MustBeArt/Zorba-composite-video/Zorba composite adapter/Zorba composite adapter.kicad_sch

## KiCad design Zorba composite adapter/Zorba composite adapter.kicad_sch (2023-02-18, an earlier design)

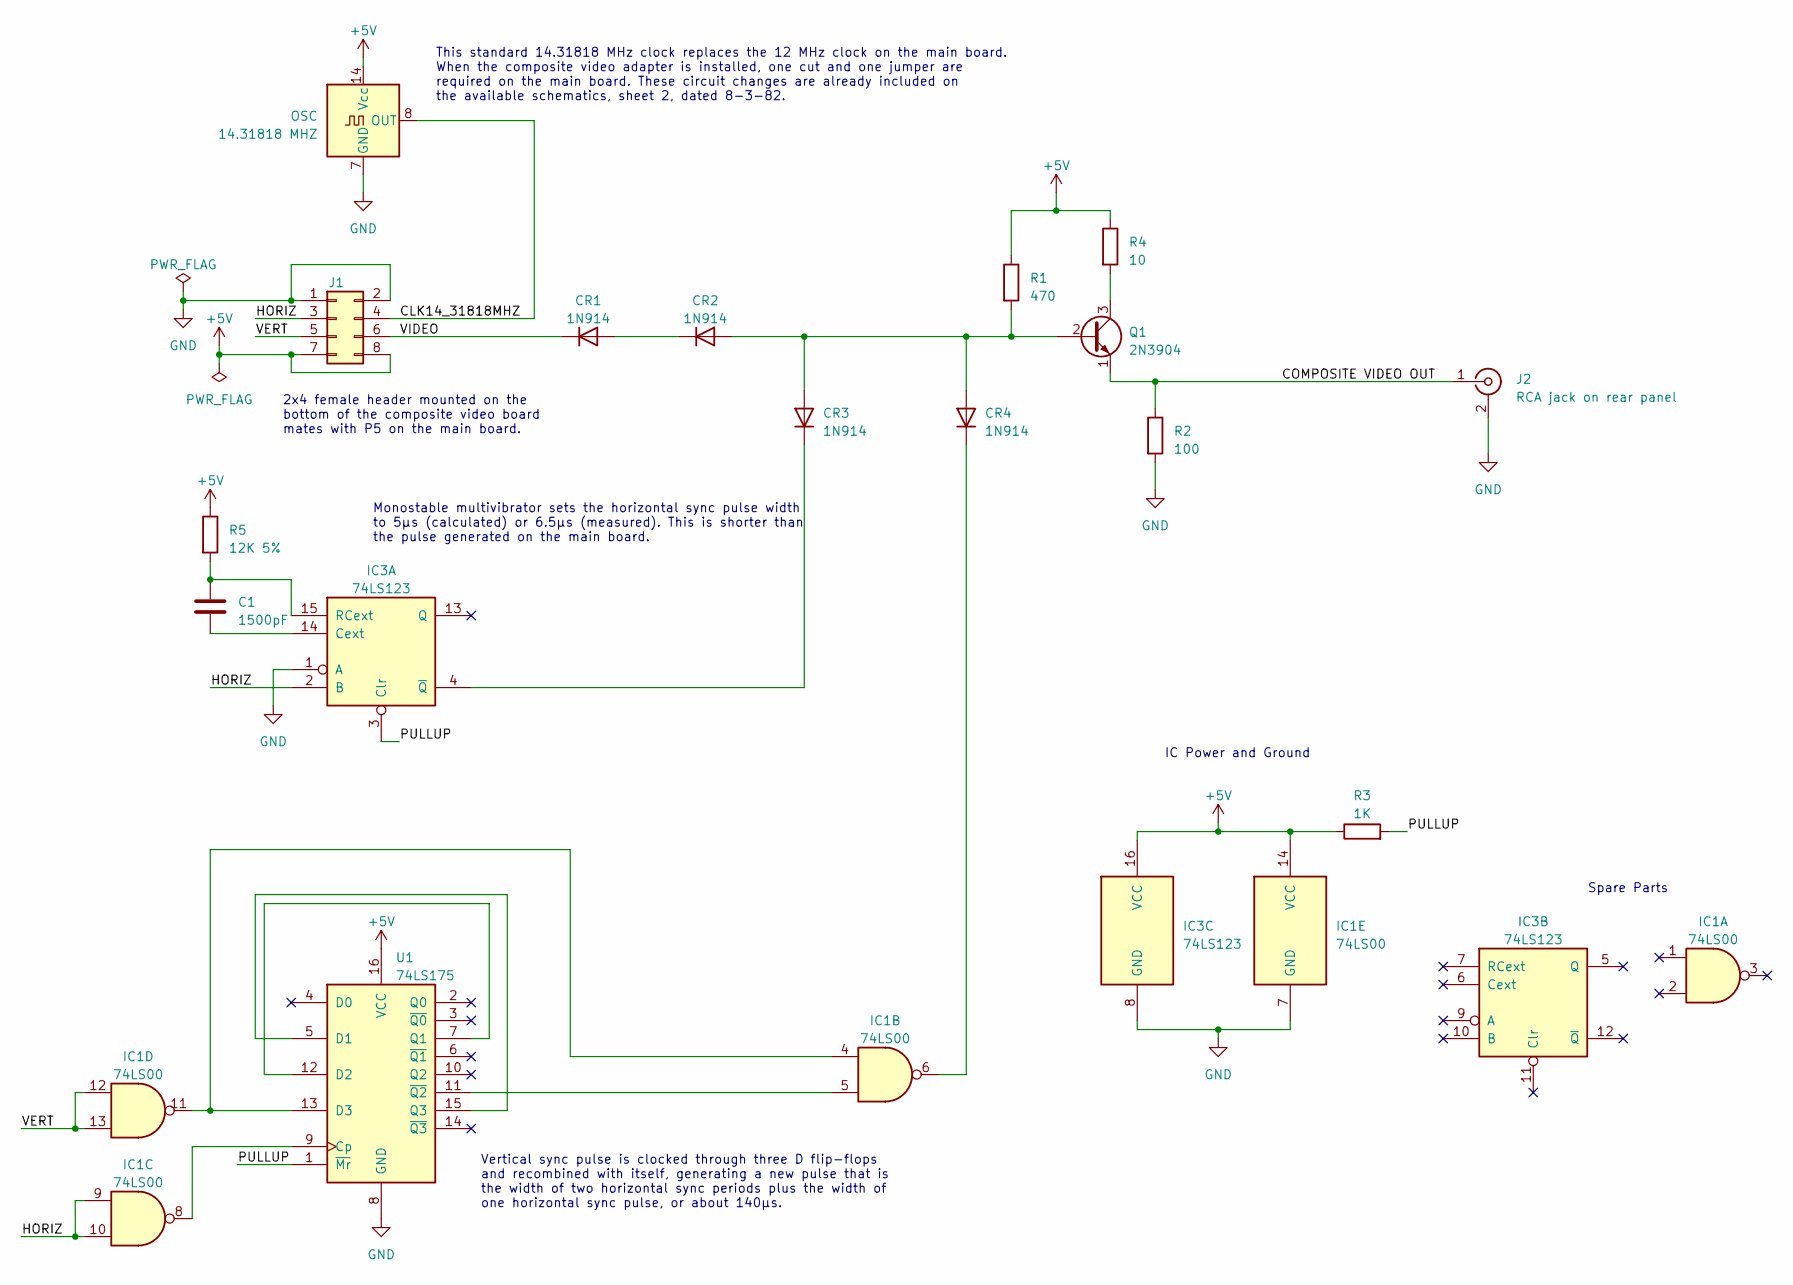
[picture p8: schematic Zorba composite adapter.kicad_sch]

Parts:
C1: 1500pF
CR1, CR2, CR3, CR4: 1N914; D_DO-35_SOD27_P7.62mm_Horizontal
IC1: 74LS00
IC3: 74LS123
J1: Conn_02x04_Odd_Even
J2: RCA jack on rear panel
OSC: 14.31818 MHZ; Oscillator_DIP-14
Q1: 2N3904; TO-92_Inline
R1: 470
R2: 100
R3: 1K
R4: 10
R5: 12K 5%
U1: 74LS175

Connections:
+5V: IC1.14 (VCC), IC3.16 (VCC), J1.7, J1.8, OSC.14 (Vcc), R1.1, R3.1, R4.1, R5.1, U1.16 (VCC)
CLK14_31818MHZ: J1.4, OSC.8 (OUT)
COMPOSITE VIDEO OUT: J2.1 (In), Q1.1 (E), R2.1
GND: IC1.7 (GND), IC3.1 (A), IC3.8 (GND), J1.1, J1.2, J2.2 (Ext), OSC.7 (GND), R2.2, U1.8 (GND)
HORIZ: IC1.9, IC1.10, IC3.2 (B), J1.3
unnamed: C1.1, IC3.15 (RCext), R5.2
unnamed: C1.2, IC3.14 (Cext)
unnamed: CR1.2 (A), CR2.1 (K)
unnamed: CR2.2 (A), CR3.2 (A), CR4.2 (A), Q1.2 (B), R1.2
unnamed: CR3.1 (K), IC3.4 (~Q)
unnamed: CR4.1 (K), IC1.6
unnamed: IC1.5, U1.11 (~Q2)
unnamed: IC1.8, U1.9 (Cp)
unnamed: IC1.4, IC1.11, U1.13 (D3)
unnamed: Q1.3 (C), R4.2
unnamed: U1.7 (Q1), U1.12 (D2)
unnamed: U1.5 (D1), U1.15 (Q3)
PULLUP: IC3.3 (Clr), R3.2, U1.1 (~Mr)
VERT: IC1.12, IC1.13, J1.5
VIDEO: CR1.1 (K), J1.6

Notes on the sheet:
IC Power and Ground
Vertical sync pulse is clocked through three D flip-flops and recombined with itself, generating a new pulse that is the width of two horizontal sync periods plus the width of one horizontal sync pulse, or about 140µs.
This standard 14.31818 MHz clock replaces the 12 MHz clock on the main board. When the composite video adapter is installed, one cut and one jumper are required on the main board. These circuit changes are already included on the available schematics, sheet 2, dated 8-3-82.
Spare Parts
Monostable multivibrator sets the horizontal sync pulse width to 5µs (calculated) or 6.5µs (measured). This is shorter than the pulse generated on the main board.
2x4 female header mounted on the bottom of the composite video board mates with P5 on the main board.
